ScionResearch/tof-proximity-sensor/src/web_server.cpp

#include "web_server.h"

WebServerManager::WebServerManager(ConfigManager* config_mgr, SensorManager* sensor_mgr) {
    config_manager = config_mgr;
    sensor_manager = sensor_mgr;
    server = new AsyncWebServer(80);
    dns_server = new DNSServer();
    session_count = 0;
    
    // Initialize session arrays
    for (int i = 0; i < 10; i++) {
        authenticated_sessions[i] = false;
        session_tokens[i] = "";
    }
}

WebServerManager::~WebServerManager() {
    delete server;
    delete dns_server;
}

bool WebServerManager::initialize() {
    // Set up basic routes
    server->on("/", HTTP_GET, [this](AsyncWebServerRequest* request) {
        handleRoot(request);
    });
    
    // iOS Captive Portal Detection routes
    server->on("/hotspot-detect.html", HTTP_GET, [this](AsyncWebServerRequest* request) {
        request->redirect("/");
    });
    
    server->on("/library/test/success.html", HTTP_GET, [this](AsyncWebServerRequest* request) {
        request->redirect("/");
    });
    
    server->on("/captive", HTTP_GET, [this](AsyncWebServerRequest* request) {
        request->redirect("/");
    });
    
    server->on("/generate_204", HTTP_GET, [this](AsyncWebServerRequest* request) {
        request->send(204);
    });
    
    server->on("/fwlink", HTTP_GET, [this](AsyncWebServerRequest* request) {
        request->redirect("/");
    });
    
    // Catch-all route for any other requests - redirect to main page
    server->onNotFound([this](AsyncWebServerRequest* request) {
        if (request->method() == HTTP_GET) {
            request->redirect("/");
        } else {
            request->send(404, "text/plain", "Not Found");
        }
    });
    
    server->on("/api/status", HTTP_GET, [this](AsyncWebServerRequest* request) {
        handleGetStatus(request);
    });
    
    server->on("/api/config", HTTP_GET, [this](AsyncWebServerRequest* request) {
        handleGetConfig(request);
    });
    
    server->on("/api/config", HTTP_POST, [this](AsyncWebServerRequest* request) {
        handleSetConfig(request);
    });
    
    server->on("/login", HTTP_GET, [this](AsyncWebServerRequest* request) {
        handleLogin(request);
    });
    
    server->on("/login", HTTP_POST, [this](AsyncWebServerRequest* request) {
        handleLogin(request);
    });
    
    server->on("/logout", HTTP_POST, [this](AsyncWebServerRequest* request) {
        handleLogout(request);
    });
    
    server->on("/api/change-password", HTTP_POST, [this](AsyncWebServerRequest* request) {
        handleChangePassword(request);
    });
    
    server->onNotFound([this](AsyncWebServerRequest* request) {
        handleNotFound(request);
    });
    
    // Initialize OTA functionality
    initializeOTA();
    
    // Start server
    server->begin();
    Serial.println("Web server started on port 80");
    return true;
}

bool WebServerManager::startAccessPoint() {
    // Get hardware MAC address before setting WiFi mode
    // Initialize WiFi first to ensure MAC address is available
    WiFi.mode(WIFI_OFF);
    delay(10);
    WiFi.mode(WIFI_STA);
    delay(100); // Give time for WiFi to initialize
    
    // Generate unique SSID based on MAC address
    uint8_t mac[6];
    WiFi.macAddress(mac);
    
    // Debug: Print full MAC address to verify uniqueness
    Serial.print("Hardware MAC Address: ");
    for (int i = 0; i < 6; i++) {
        if (i > 0) Serial.print(":");
        if (mac[i] < 16) Serial.print("0");
        Serial.print(mac[i], HEX);
    }
    Serial.println();
    
    // Use last 3 bytes for SSID (bytes 3, 4, 5)
    String unique_ssid = "ToF-Prox-";
    if (mac[3] < 16) unique_ssid += "0";
    unique_ssid += String(mac[3], HEX);
    if (mac[4] < 16) unique_ssid += "0";
    unique_ssid += String(mac[4], HEX);
    if (mac[5] < 16) unique_ssid += "0";
    unique_ssid += String(mac[5], HEX);
    unique_ssid.toUpperCase();
    
    WiFiConfig wifi_config = config_manager->getWiFiConfig();
    
    // Configure AP with specific settings for better iOS compatibility
    WiFi.mode(WIFI_AP);
    WiFi.softAPConfig(IPAddress(192, 168, 4, 1), IPAddress(192, 168, 4, 1), IPAddress(255, 255, 255, 0));
    
    // Start AP with specific settings: channel 1, no SSID hidden, max 4 connections
    bool success = WiFi.softAP(unique_ssid.c_str(), wifi_config.ap_password, 1, 0, 4);
    
    if (success) {
        // Additional iOS compatibility settings
        delay(100); // Small delay for AP to stabilize
        WiFi.softAPsetHostname("proximity-sensor");
    }
    
    if (success) {
        IPAddress ip = WiFi.softAPIP();
        Serial.print("Access Point started: ");
        Serial.println(unique_ssid);
        Serial.print("IP address: ");
        Serial.println(ip);
        
        // Start DNS server for captive portal
        dns_server->start(53, "*", ip);
        Serial.println("DNS server started for captive portal");
        
        return true;
    }
    
    Serial.println("Failed to start Access Point");
    return false;
}

void WebServerManager::stopAccessPoint() {
    WiFi.softAPdisconnect(true);
    Serial.println("Access Point stopped");
}

void WebServerManager::handleClient() {
    // Process DNS requests for captive portal
    dns_server->processNextRequest();
}

String WebServerManager::generateSessionToken() {
    String token = "";
    for (int i = 0; i < 16; i++) {
        token += String(random(0, 16), HEX);
    }
    return token;
}

void WebServerManager::addSession(const String& token) {
    for (int i = 0; i < 10; i++) {
        if (!authenticated_sessions[i]) {
            authenticated_sessions[i] = true;
            session_tokens[i] = token;
            session_count++;
            break;
        }
    }
}

bool WebServerManager::validateSession(const String& token) {
    for (int i = 0; i < 10; i++) {
        if (authenticated_sessions[i] && session_tokens[i] == token) {
            return true;
        }
    }
    return false;
}

bool WebServerManager::isAuthenticated(AsyncWebServerRequest* request) {
    if (request->hasHeader("Cookie")) {
        String cookie = request->header("Cookie");
        int tokenStart = cookie.indexOf("session_token=");
        if (tokenStart != -1) {
            tokenStart += 14; // Length of "session_token="
            int tokenEnd = cookie.indexOf(";", tokenStart);
            if (tokenEnd == -1) tokenEnd = cookie.length();
            String token = cookie.substring(tokenStart, tokenEnd);
            return validateSession(token);
        }
    }
    return false;
}

void WebServerManager::handleRoot(AsyncWebServerRequest* request) {
    if (!isAuthenticated(request)) {
        handleLogin(request);
        return;
    }
    
    String html = generateMainPage();
    AsyncWebServerResponse* response = request->beginResponse(200, "text/html", html);
    
    // Add iOS-friendly headers
    response->addHeader("Cache-Control", "no-cache, no-store, must-revalidate");
    response->addHeader("Pragma", "no-cache");
    response->addHeader("Expires", "0");
    response->addHeader("Connection", "close");
    
    request->send(response);
}

String WebServerManager::generateMainPage() {
    String html = "<!DOCTYPE html>";
    html += "<html><head><title>Proximity Sensor</title>";
    html += "<meta name='viewport' content='width=device-width, initial-scale=1'>";
    html += "<style>";
    html += "body { font-family: Arial; margin: 0; background:rgb(27, 27, 27); }";
    html += ".page-header { background:rgb(27, 27, 27); padding: 20px; text-align: center; }";
    html += ".header-logo img { max-width: 400px; height: auto; }";
    html += ".container { max-width: 800px; margin: 0 auto; background: white; padding: 20px; border-radius: 10px 10px 0 0; }";
    html += ".status-grid { display: grid; grid-template-columns: repeat(auto-fit, minmax(180px, 1fr)); gap: 15px; margin: 20px 0; }";
    html += ".status-card { background: #f8f9fa; padding: 15px; border-radius: 8px; text-align: center; border: 2px solid #e9ecef; min-height: 80px; display: flex; flex-direction: column; justify-content: center; }";
    html += ".status-value { font-size: 2em; font-weight: bold; color: #007bff; margin: 5px 0; }";
    html += ".refresh-btn { background: #007bff; color: white; border: none; padding: 10px 20px; border-radius: 5px; cursor: pointer; margin: 10px 5px; }";
    html += ".refresh-btn:hover { background: #0056b3; }";
    html += ".config-section { margin-top: 30px; padding: 20px; background: #f8f9fa; border-radius: 10px; }";
    html += ".output-config { margin: 20px 0; padding: 20px; background: white; border-radius: 8px; border: 1px solid #dee2e6; }";
    html += ".form-grid { display: grid; grid-template-columns: 1fr 200px; gap: 15px; align-items: center; margin: 12px 0; }";
    html += ".form-grid label { font-weight: bold; margin: 0; }";
    html += ".form-grid input, .form-grid select { width: 100%; padding: 8px; border: 1px solid #ced4da; border-radius: 4px; box-sizing: border-box; }";
    html += ".output-header { display: flex; align-items: center; justify-content: space-between; margin-bottom: 20px; padding-bottom: 10px; border-bottom: 2px solid #e9ecef; }";
    html += ".output-header h4 { margin: 0; color: #495057; }";
    html += ".enable-control { display: flex; align-items: center; gap: 10px; }";
    html += ".enable-control input[type='checkbox'] { transform: scale(1.3); margin: 0; }";
    html += ".config-btn { background: #28a745; color: white; border: none; padding: 12px 24px; border-radius: 5px; cursor: pointer; margin: 15px 5px; font-size: 16px; }";
    html += ".config-btn:hover { background: #218838; }";
    html += "#config-message { margin: 15px 0; padding: 10px; border-radius: 5px; display: none; }";
    html += ".success { background: #d4edda; color: #155724; border: 1px solid #c3e6cb; }";
    html += ".error { background: #f8d7da; color: #721c24; border: 1px solid #f5c6cb; }";
    html += ".logout-btn { background: #dc3545; color: white; border: none; padding: 8px 16px; border-radius: 5px; cursor: pointer; }";
    html += ".logout-btn:hover { background: #c82333; }";
    html += "@media (max-width: 600px) { .form-grid { grid-template-columns: 1fr; gap: 8px; } .form-grid label { margin-bottom: 5px; } .header-logo img { max-width: 400px; } }";
    html += "</style></head><body>";
    html += "<div class='page-header'>";
    html += "<div class='header-logo'>";
    html += "<img src=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 />";
    html += "</div>";
    html += "</div>";
    html += "<div class='container'>";
    html += "<h1>Proximity Sensor Monitor</h1>";
    html += "<div class='status-grid'>";
    html += "<div class='status-card'><h3>Distance</h3><div class='status-value' id='distance'>--</div><div>mm</div></div>";
    html += "<div class='status-card'><h3>Status</h3><div id='status'>--</div></div>";
    html += "<div class='status-card'><h3>Output 1</h3><div id='output1'>--</div></div>";
    html += "<div class='status-card'><h3>Output 2</h3><div id='output2'>--</div></div>";
    html += "</div>";
    html += "<div id='config-info'><h3>Current Configuration</h3><div id='config-display'>Loading...</div></div>";
    html += "<div class='config-section'>";
    html += "<h3>Output Configuration</h3>";
    html += "<form id='config-form'>";
    html += "<div class='output-config'>";
    html += "<div class='output-header'>";
    html += "<h4>Output 1</h4>";
    html += "<div class='enable-control'>";
    html += "<span>Enable</span>";
    html += "<input type='checkbox' id='output1_enabled' name='output1_enabled'>";
    html += "</div>";
    html += "</div>";
    html += "<div class='form-grid'>";
    html += "<label>Min Distance (mm):</label>";
    html += "<input type='number' id='output1_min' name='output1_min' min='0' max='4000'>";
    html += "</div>";
    html += "<div class='form-grid'>";
    html += "<label>Max Distance (mm):</label>";
    html += "<input type='number' id='output1_max' name='output1_max' min='0' max='4000'>";
    html += "</div>";
    html += "<div class='form-grid'>";
    html += "<label>Hysteresis (mm):</label>";
    html += "<input type='number' id='output1_hysteresis' name='output1_hysteresis' min='0' max='500'>";
    html += "</div>";
    html += "<div class='form-grid'>";
    html += "<label>Polarity:</label>";
    html += "<select id='output1_polarity' name='output1_polarity'><option value='in_range'>Active In Range</option><option value='out_range'>Active Out of Range</option></select>";
    html += "</div>";
    html += "</div>";
    html += "<div class='output-config'>";
    html += "<div class='output-header'>";
    html += "<h4>Output 2</h4>";
    html += "<div class='enable-control'>";
    html += "<span>Enable</span>";
    html += "<input type='checkbox' id='output2_enabled' name='output2_enabled'>";
    html += "</div>";
    html += "</div>";
    html += "<div class='form-grid'>";
    html += "<label>Min Distance (mm):</label>";
    html += "<input type='number' id='output2_min' name='output2_min' min='0' max='4000'>";
    html += "</div>";
    html += "<div class='form-grid'>";
    html += "<label>Max Distance (mm):</label>";
    html += "<input type='number' id='output2_max' name='output2_max' min='0' max='4000'>";
    html += "</div>";
    html += "<div class='form-grid'>";
    html += "<label>Hysteresis (mm):</label>";
    html += "<input type='number' id='output2_hysteresis' name='output2_hysteresis' min='0' max='500'>";
    html += "</div>";
    html += "<div class='form-grid'>";
    html += "<label>Polarity:</label>";
    html += "<select id='output2_polarity' name='output2_polarity'><option value='in_range'>Active In Range</option><option value='out_range'>Active Out of Range</option></select>";
    html += "</div>";
    html += "</div>";
    html += "<button type='button' class='config-btn' onclick='saveConfig()'>Save Configuration</button>";
    html += "</form>";
    html += "<div id='config-message'></div>";
    html += "</div>";
    html += "<div class='config-section'>";
    html += "<h3>Change Password</h3>";
    html += "<form id='password-form'>";
    html += "<div class='output-config'>";
    html += "<div class='form-grid'>";
    html += "<label>Current Password:</label>";
    html += "<input type='password' id='current_password' name='current_password' required>";
    html += "</div>";
    html += "<div class='form-grid'>";
    html += "<label>New Password:</label>";
    html += "<input type='password' id='new_password' name='new_password' required>";
    html += "</div>";
    html += "<div class='form-grid'>";
    html += "<label>Confirm New Password:</label>";
    html += "<input type='password' id='confirm_password' name='confirm_password' required>";
    html += "</div>";
    html += "<button type='button' class='config-btn' onclick='changePassword()'>Change Password</button>";
    html += "</div>";
    html += "</form>";
    html += "<div id='password-message'></div>";
    html += "</div>";
    html += "<div class='config-section'>";
    html += "<h3>Firmware Update (OTA)</h3>";
    html += "<div class='output-config'>";
    html += "<p style='color: #856404; background: #fff3cd; padding: 10px; border-radius: 5px; border: 1px solid #ffeaa7;'>";
    html += "<strong>Warning:</strong> Only upload firmware files (.bin) intended for this device. ";
    html += "Incorrect firmware can permanently damage the device.";
    html += "</p>";
    html += "<p><strong>Version:   </strong> " + String(FW_VERSION) + "</p>";
    html += "<p><strong>Build Date:</strong> " + String(__DATE__) + " " + String(__TIME__) + "</p>";
    html += "<button type='button' class='config-btn' onclick='openOTAUpdate()' style='background: #fd7e14;'>";
    html += "Open Firmware Update";
    html += "</button>";
    html += "</div>";
    html += "</div>";
    html += "<div style='text-align: center; margin-top: 30px; padding-top: 20px; border-top: 1px solid #dee2e6;'>";
    html += "<button class='logout-btn' onclick='logout()'>Logout</button>";
    html += "</div>";
    html += "</div>";
    html += "<script>";
    html += "function updateStatus() {";
    html += "fetch('/api/status').then(response => response.json()).then(data => {";
    html += "document.getElementById('distance').textContent = data.out_of_range ? 'Out of range' : data.distance;";
    html += "document.getElementById('status').textContent = data.status;";
    html += "document.getElementById('output1').textContent = data.output1_state ? 'ON' : 'OFF';";
    html += "document.getElementById('output2').textContent = data.output2_state ? 'ON' : 'OFF';";
    html += "const statusCard = document.getElementById('status').parentElement;";
    html += "const output1Card = document.getElementById('output1').parentElement;";
    html += "const output2Card = document.getElementById('output2').parentElement;";
    html += "if (data.status === 'OK') {";
    html += "statusCard.style.backgroundColor = '#e8f5e8';";
    html += "} else if (data.status === 'TRIGGERED') {";
    html += "statusCard.style.backgroundColor = '#e3f2fd';";
    html += "} else if (data.status === 'FAULT') {";
    html += "statusCard.style.backgroundColor = '#ffebee';";
    html += "} else {";
    html += "statusCard.style.backgroundColor = '#f8f9fa';";
    html += "}";
    html += "output1Card.style.backgroundColor = data.output1_state ? '#e3f2fd' : '#f8f9fa';";
    html += "output2Card.style.backgroundColor = data.output2_state ? '#e3f2fd' : '#f8f9fa';";
    html += "}).catch(error => console.error('Error:', error));";
    html += "}";
    html += "function loadConfig() {";
    html += "fetch('/api/config').then(response => response.json()).then(data => {";
    html += "const configHtml = '<p><strong>Device:</strong> ' + data.device_name + '</p>' +";
    html += "'<p><strong>Output 1:</strong> ' + (data.output1.enabled ? 'Enabled' : 'Disabled') + ' - ' + data.output1.min + '-' + data.output1.max + 'mm, Hyst: ' + data.output1.hysteresis + 'mm (' + (data.output1.active_in_range ? 'In Range' : 'Out of Range') + ')</p>' +";
    html += "'<p><strong>Output 2:</strong> ' + (data.output2.enabled ? 'Enabled' : 'Disabled') + ' - ' + data.output2.min + '-' + data.output2.max + 'mm, Hyst: ' + data.output2.hysteresis + 'mm (' + (data.output2.active_in_range ? 'In Range' : 'Out of Range') + ')</p>';";
    html += "document.getElementById('config-display').innerHTML = configHtml;";
    html += "document.getElementById('output1_enabled').checked = data.output1.enabled;";
    html += "document.getElementById('output1_min').value = data.output1.min;";
    html += "document.getElementById('output1_max').value = data.output1.max;";
    html += "document.getElementById('output1_hysteresis').value = data.output1.hysteresis;";
    html += "document.getElementById('output1_polarity').value = data.output1.active_in_range ? 'in_range' : 'out_range';";
    html += "document.getElementById('output2_enabled').checked = data.output2.enabled;";
    html += "document.getElementById('output2_min').value = data.output2.min;";
    html += "document.getElementById('output2_max').value = data.output2.max;";
    html += "document.getElementById('output2_hysteresis').value = data.output2.hysteresis;";
    html += "document.getElementById('output2_polarity').value = data.output2.active_in_range ? 'in_range' : 'out_range';";
    html += "}).catch(error => console.error('Error:', error));";
    html += "}";
    html += "function saveConfig() {";
    html += "const formData = new FormData();";
    html += "formData.append('output1_enabled', document.getElementById('output1_enabled').checked ? '1' : '0');";
    html += "formData.append('output1_min', document.getElementById('output1_min').value);";
    html += "formData.append('output1_max', document.getElementById('output1_max').value);";
    html += "formData.append('output1_hysteresis', document.getElementById('output1_hysteresis').value);";
    html += "formData.append('output1_polarity', document.getElementById('output1_polarity').value);";
    html += "formData.append('output2_enabled', document.getElementById('output2_enabled').checked ? '1' : '0');";
    html += "formData.append('output2_min', document.getElementById('output2_min').value);";
    html += "formData.append('output2_max', document.getElementById('output2_max').value);";
    html += "formData.append('output2_hysteresis', document.getElementById('output2_hysteresis').value);";
    html += "formData.append('output2_polarity', document.getElementById('output2_polarity').value);";
    html += "fetch('/api/config', { method: 'POST', body: formData })";
    html += ".then(response => response.json()).then(data => {";
    html += "const msgDiv = document.getElementById('config-message');";
    html += "msgDiv.style.display = 'block';";
    html += "if (data.status === 'success') {";
    html += "msgDiv.className = 'success';";
    html += "msgDiv.textContent = 'Configuration saved successfully!';";
    html += "loadConfig();";
    html += "} else {";
    html += "msgDiv.className = 'error';";
    html += "msgDiv.textContent = 'Error: ' + data.message;";
    html += "}";
    html += "setTimeout(() => msgDiv.style.display = 'none', 3000);";
    html += "}).catch(error => {";
    html += "const msgDiv = document.getElementById('config-message');";
    html += "msgDiv.style.display = 'block';";
    html += "msgDiv.className = 'error';";
    html += "msgDiv.textContent = 'Network error: ' + error.message;";
    html += "setTimeout(() => msgDiv.style.display = 'none', 3000);";
    html += "});";
    html += "}";
    html += "function logout() {";
    html += "fetch('/logout', { method: 'POST' }).then(() => {";
    html += "window.location.href = '/login';";
    html += "});";
    html += "}";
    html += "function changePassword() {";
    html += "const newPassword = document.getElementById('new_password').value;";
    html += "const confirmPassword = document.getElementById('confirm_password').value;";
    html += "if (newPassword !== confirmPassword) {";
    html += "const msgDiv = document.getElementById('password-message');";
    html += "msgDiv.style.display = 'block';";
    html += "msgDiv.className = 'error';";
    html += "msgDiv.textContent = 'New passwords do not match!';";
    html += "setTimeout(() => msgDiv.style.display = 'none', 3000);";
    html += "return;";
    html += "}";
    html += "const formData = new FormData();";
    html += "formData.append('current_password', document.getElementById('current_password').value);";
    html += "formData.append('new_password', newPassword);";
    html += "fetch('/api/change-password', { method: 'POST', body: formData })";
    html += ".then(response => response.json()).then(data => {";
    html += "const msgDiv = document.getElementById('password-message');";
    html += "msgDiv.style.display = 'block';";
    html += "if (data.status === 'success') {";
    html += "msgDiv.className = 'success';";
    html += "msgDiv.textContent = 'Password changed successfully!';";
    html += "document.getElementById('current_password').value = '';";
    html += "document.getElementById('new_password').value = '';";
    html += "document.getElementById('confirm_password').value = '';";
    html += "} else {";
    html += "msgDiv.className = 'error';";
    html += "msgDiv.textContent = 'Error: ' + data.message;";
    html += "}";
    html += "setTimeout(() => msgDiv.style.display = 'none', 3000);";
    html += "}).catch(error => {";
    html += "const msgDiv = document.getElementById('password-message');";
    html += "msgDiv.style.display = 'block';";
    html += "msgDiv.className = 'error';";
    html += "msgDiv.textContent = 'Network error: ' + error.message;";
    html += "setTimeout(() => msgDiv.style.display = 'none', 3000);";
    html += "});";
    html += "}";
    html += "function openOTAUpdate() {";
    html += "if (confirm('Are you sure you want to open the firmware update page? Make sure you have the correct firmware file ready.')) {";
    html += "window.open('/update', '_blank');";
    html += "}";
    html += "}";
    html += "function detectMobileAndHideFirmware() {";
    html += "const userAgent = navigator.userAgent.toLowerCase();";
    html += "const isMobile = /android|webos|iphone|ipad|ipod|blackberry|iemobile|opera mini|mobile/.test(userAgent);";
    html += "const firmwareSections = document.querySelectorAll('.config-section');";
    html += "for(let section of firmwareSections) {";
    html += "if(section.innerHTML.includes('Firmware Update')) {";
    html += "if(isMobile) section.style.display = 'none';";
    html += "break;";
    html += "}";
    html += "}";
    html += "}";
    html += "detectMobileAndHideFirmware();";
    html += "setInterval(updateStatus, 200);";
    html += "updateStatus(); loadConfig();";
    html += "</script></body></html>";
    
    return html;
}

void WebServerManager::handleGetStatus(AsyncWebServerRequest* request) {
    if (!isAuthenticated(request)) {
        request->send(401, "application/json", "{\"error\":\"Unauthorized\"}");
        return;
    }
    
    JsonDocument doc;
    doc["distance"] = sensor_manager->getDistance();
    doc["raw_distance"] = sensor_manager->getRawDistance();
    doc["sensor_ready"] = sensor_manager->isSensorReady();
    doc["out_of_range"] = sensor_manager->isOutOfRange();
    
    switch (sensor_manager->getStatus()) {
        case STATUS_OK:
            doc["status"] = "OK";
            break;
        case STATUS_TRIGGERED:
            doc["status"] = "TRIGGERED";
            break;
        case STATUS_FAULT:
            doc["status"] = "FAULT";
            break;
    }
    
    doc["output1_state"] = sensor_manager->getOutput1Config().current_state;
    doc["output2_state"] = sensor_manager->getOutput2Config().current_state;
    doc["timestamp"] = millis();
    
    String response;
    serializeJson(doc, response);
    AsyncWebServerResponse* res = request->beginResponse(200, "application/json", response);
    res->addHeader("Cache-Control", "no-cache, no-store, must-revalidate");
    res->addHeader("Pragma", "no-cache");
    res->addHeader("Expires", "0");
    res->addHeader("Connection", "close");
    request->send(res);
}

void WebServerManager::handleGetConfig(AsyncWebServerRequest* request) {
    if (!isAuthenticated(request)) {
        request->send(401, "application/json", "{\"error\":\"Unauthorized\"}");
        return;
    }
    
    String config = config_manager->getConfigJson();
    AsyncWebServerResponse* res = request->beginResponse(200, "application/json", config);
    res->addHeader("Cache-Control", "no-cache, no-store, must-revalidate");
    res->addHeader("Pragma", "no-cache");
    res->addHeader("Expires", "0");
    res->addHeader("Connection", "close");
    request->send(res);
}

void WebServerManager::handleNotFound(AsyncWebServerRequest* request) {
    request->send(404, "text/plain", "Not Found");
}

void WebServerManager::handleLogin(AsyncWebServerRequest* request) {
    if (request->method() == HTTP_GET) {
        // Show login form
        String html = "<!DOCTYPE html><html><head><title>Login - Proximity Sensor</title>";
        html += "<meta name='viewport' content='width=device-width, initial-scale=1'>";
        html += "<style>";
        html += "body { font-family: Arial; margin: 0; padding: 0; background: #f0f0f0; display: flex; justify-content: center; align-items: center; min-height: 100vh; }";
        html += ".login-container { background: white; padding: 40px; border-radius: 10px; box-shadow: 0 4px 6px rgba(0,0,0,0.1); max-width: 400px; width: 100%; }";
        html += "h1 { text-align: center; color: #333; margin-bottom: 30px; }";
        html += "label { display: block; margin: 15px 0 5px; font-weight: bold; }";
        html += "input[type='password'] { width: 100%; padding: 12px; border: 1px solid #ddd; border-radius: 5px; font-size: 16px; box-sizing: border-box; }";
        html += ".login-btn { width: 100%; background: #007bff; color: white; border: none; padding: 12px; border-radius: 5px; font-size: 16px; cursor: pointer; margin-top: 20px; }";
        html += ".login-btn:hover { background: #0056b3; }";
        html += ".error { color: #dc3545; text-align: center; margin-top: 15px; }";
        html += "</style></head><body>";
        html += "<div class='login-container'>";
        html += "<h1>Proximity Sensor Login</h1>";
        html += "<form method='POST' action='/login'>";
        html += "<label for='password'>Password:</label>";
        html += "<input type='password' id='password' name='password' required>";
        html += "<button type='submit' class='login-btn'>Login</button>";
        html += "</form>";
        if (request->hasParam("error")) {
            html += "<div class='error'>Invalid password. Please try again.</div>";
        }
        html += "</div></body></html>";
        
        AsyncWebServerResponse* response = request->beginResponse(200, "text/html", html);
        // Add iOS-friendly headers
        response->addHeader("Cache-Control", "no-cache, no-store, must-revalidate");
        response->addHeader("Pragma", "no-cache");
        response->addHeader("Expires", "0");
        response->addHeader("Connection", "close");
        request->send(response);
    } else {
        // Process login
        if (request->hasParam("password", true)) {
            String password = request->getParam("password", true)->value();
            WiFiConfig wifi_config = config_manager->getWiFiConfig();
            
            if (password == wifi_config.admin_password) {
                // Generate session token
                String token = generateSessionToken();
                addSession(token);
                
                // Set cookie and redirect
                AsyncWebServerResponse* response = request->beginResponse(302);
                response->addHeader("Location", "/");
                response->addHeader("Set-Cookie", "session_token=" + token + "; Path=/; HttpOnly");
                request->send(response);
            } else {
                request->redirect("/login?error=1");
            }
        } else {
            request->redirect("/login?error=1");
        }
    }
}

void WebServerManager::handleLogout(AsyncWebServerRequest* request) {
    // Clear session
    if (request->hasHeader("Cookie")) {
        String cookie = request->header("Cookie");
        int tokenStart = cookie.indexOf("session_token=");
        if (tokenStart != -1) {
            tokenStart += 14;
            int tokenEnd = cookie.indexOf(";", tokenStart);
            if (tokenEnd == -1) tokenEnd = cookie.length();
            String token = cookie.substring(tokenStart, tokenEnd);
            
            // Remove session
            for (int i = 0; i < 10; i++) {
                if (session_tokens[i] == token) {
                    authenticated_sessions[i] = false;
                    session_tokens[i] = "";
                    break;
                }
            }
        }
    }
    
    // Clear cookie and redirect
    AsyncWebServerResponse* response = request->beginResponse(302);
    response->addHeader("Location", "/login");
    response->addHeader("Set-Cookie", "session_token=; Path=/; HttpOnly; Max-Age=0");
    request->send(response);
}

void WebServerManager::handleChangePassword(AsyncWebServerRequest* request) {
    if (!isAuthenticated(request)) {
        request->send(401, "application/json", "{\"error\":\"Unauthorized\"}");
        return;
    }
    
    if (request->hasParam("current_password", true) && request->hasParam("new_password", true)) {
        String current_password = request->getParam("current_password", true)->value();
        String new_password = request->getParam("new_password", true)->value();
        
        WiFiConfig wifi_config = config_manager->getWiFiConfig();
        
        if (current_password == wifi_config.admin_password) {
            wifi_config.admin_password = new_password;
            config_manager->setWiFiConfig(wifi_config);
            config_manager->saveConfig();
            
            Serial.println("Admin password changed via web interface");
            request->send(200, "application/json", "{\"status\":\"success\",\"message\":\"Password changed successfully\"}");
        } else {
            request->send(400, "application/json", "{\"status\":\"error\",\"message\":\"Current password is incorrect\"}");
        }
    } else {
        request->send(400, "application/json", "{\"status\":\"error\",\"message\":\"Missing required parameters\"}");
    }
}
void WebServerManager::handleSetConfig(AsyncWebServerRequest* request) {
    if (!isAuthenticated(request)) {
        request->send(401, "application/json", "{\"error\":\"Unauthorized\"}");
        return;
    }
    
    // Parse form data from POST request
    bool config_changed = false;
    DeviceConfig current_config = config_manager->getDeviceConfig();
    
    // Output 1 configuration
    if (request->hasParam("output1_enabled", true)) {
        bool new_enabled = request->getParam("output1_enabled", true)->value() == "1";
        if (new_enabled != current_config.output1_enabled) {
            current_config.output1_enabled = new_enabled;
            config_changed = true;
        }
    }
    
    if (request->hasParam("output1_min", true)) {
        int new_min = request->getParam("output1_min", true)->value().toInt();
        if (new_min != current_config.output1_min) {
            current_config.output1_min = new_min;
            config_changed = true;
        }
    }
    
    if (request->hasParam("output1_max", true)) {
        int new_max = request->getParam("output1_max", true)->value().toInt();
        if (new_max != current_config.output1_max) {
            current_config.output1_max = new_max;
            config_changed = true;
        }
    }
    
    if (request->hasParam("output1_hysteresis", true)) {
        int new_hyst = request->getParam("output1_hysteresis", true)->value().toInt();
        if (new_hyst != current_config.output1_hysteresis) {
            current_config.output1_hysteresis = new_hyst;
            config_changed = true;
        }
    }
    
    if (request->hasParam("output1_polarity", true)) {
        bool new_polarity = request->getParam("output1_polarity", true)->value() == "in_range";
        if (new_polarity != current_config.output1_active_in_range) {
            current_config.output1_active_in_range = new_polarity;
            config_changed = true;
        }
    }
    
    // Output 2 configuration
    if (request->hasParam("output2_enabled", true)) {
        bool new_enabled = request->getParam("output2_enabled", true)->value() == "1";
        if (new_enabled != current_config.output2_enabled) {
            current_config.output2_enabled = new_enabled;
            config_changed = true;
        }
    }
    
    if (request->hasParam("output2_min", true)) {
        int new_min = request->getParam("output2_min", true)->value().toInt();
        if (new_min != current_config.output2_min) {
            current_config.output2_min = new_min;
            config_changed = true;
        }
    }
    
    if (request->hasParam("output2_max", true)) {
        int new_max = request->getParam("output2_max", true)->value().toInt();
        if (new_max != current_config.output2_max) {
            current_config.output2_max = new_max;
            config_changed = true;
        }
    }
    
    if (request->hasParam("output2_hysteresis", true)) {
        int new_hyst = request->getParam("output2_hysteresis", true)->value().toInt();
        if (new_hyst != current_config.output2_hysteresis) {
            current_config.output2_hysteresis = new_hyst;
            config_changed = true;
        }
    }
    
    if (request->hasParam("output2_polarity", true)) {
        bool new_polarity = request->getParam("output2_polarity", true)->value() == "in_range";
        if (new_polarity != current_config.output2_active_in_range) {
            current_config.output2_active_in_range = new_polarity;
            config_changed = true;
        }
    }
    
    // Apply changes if any were made
    if (config_changed) {
        config_manager->setDeviceConfig(current_config);
        config_manager->saveConfig();
        
        // Update sensor manager with new configuration
        sensor_manager->updateConfiguration(current_config);
        
        Serial.println("Configuration updated via web interface");
        request->send(200, "application/json", "{\"status\":\"success\",\"message\":\"Configuration updated\"}");
    } else {
        request->send(200, "application/json", "{\"status\":\"no_change\",\"message\":\"No changes detected\"}");
    }
}
void WebServerManager::handleGetHistory(AsyncWebServerRequest* request) {}
void WebServerManager::handleClearHistory(AsyncWebServerRequest* request) {}
void WebServerManager::handleResetConfig(AsyncWebServerRequest* request) {}

// OTA Update Implementation
void WebServerManager::initializeOTA() {
    // Add OTA update page route
    server->on("/update", HTTP_GET, [this](AsyncWebServerRequest* request) {
        handleOTAUpdate(request);
    });
    
    // Add OTA upload handler
    server->on("/update", HTTP_POST, 
        [this](AsyncWebServerRequest* request) {
            // Handle the response after upload completes
            if (Update.hasError()) {
                request->send(500, "text/plain", "Update Failed: " + String(Update.getError()));
            } else {
                request->send(200, "text/plain", "Update Successful! Rebooting...");
                delay(1000);
                ESP.restart();
            }
        },
        [this](AsyncWebServerRequest* request, String filename, size_t index, uint8_t* data, size_t len, bool final) {
            handleOTAUpload(request, filename, index, data, len, final);
        }
    );
    
    Serial.println("OTA Update service initialized");
    Serial.println("Access OTA update at: http://[device-ip]/update");
}

void WebServerManager::handleOTAUpdate(AsyncWebServerRequest* request) {
    // Check authentication
    if (!isAuthenticated(request)) {
        request->redirect("/login");
        return;
    }
    
    // Generate OTA update page
    String html = "<!DOCTYPE html><html><head>";
    html += "<title>Firmware Update - Proximity Sensor</title>";
    html += "<meta name='viewport' content='width=device-width, initial-scale=1'>";
    html += "<style>";
    html += "body { font-family: Arial, sans-serif; margin: 0; padding: 20px; background: #f5f5f5; }";
    html += ".container { max-width: 600px; margin: 0 auto; background: white; padding: 30px; border-radius: 10px; box-shadow: 0 2px 10px rgba(0,0,0,0.1); }";
    html += "h1 { color: #333; text-align: center; margin-bottom: 30px; }";
    html += ".warning { background: #fff3cd; color: #856404; padding: 15px; border-radius: 5px; border: 1px solid #ffeaa7; margin-bottom: 20px; }";
    html += ".upload-section { background: #f8f9fa; padding: 20px; border-radius: 5px; margin: 20px 0; }";
    html += "input[type='file'] { width: 100%; padding: 10px; margin: 10px 0; border: 2px dashed #ccc; border-radius: 5px; }";
    html += ".btn { background: #007bff; color: white; border: none; padding: 12px 24px; border-radius: 5px; cursor: pointer; font-size: 16px; width: 100%; }";
    html += ".btn:hover { background: #0056b3; }";
    html += ".btn:disabled { background: #6c757d; cursor: not-allowed; }";
    html += "#progress { width: 100%; height: 20px; background: #e9ecef; border-radius: 10px; margin: 20px 0; overflow: hidden; }";
    html += "#progress-bar { height: 100%; background: #28a745; width: 0%; transition: width 0.3s; }";
    html += ".back-btn { background: #6c757d; margin-top: 20px; }";
    html += ".back-btn:hover { background: #545b62; }";
    html += "</style></head><body>";
    html += "<div class='container'>";
    html += "<h1>Firmware Update</h1>";
    html += "<div class='warning'>";
    html += "<strong>Warning:</strong> Only upload firmware files (.bin) intended for this device. ";
    html += "Incorrect firmware can permanently damage the device. Ensure you have a stable power supply during the update.";
    html += "</div>";
    html += "<div class='upload-section'>";
    html += "<h3>Current Firmware</h3>";
    html += "<p><strong>Version:   </strong> " + String(FW_VERSION) + "</p>";
    html += "<p><strong>Build Date:</strong> " + String(__DATE__) + " " + String(__TIME__) + "</p>";
    html += "<p><strong>Free Space:</strong> " + String(ESP.getFreeSketchSpace()) + " bytes</p>";
    html += "</div>";
    html += "<form id='upload-form' enctype='multipart/form-data'>";
    html += "<h3>Select Firmware File</h3>";
    html += "<input type='file' id='firmware-file' accept='.bin' required>";
    html += "<button type='submit' class='btn' id='upload-btn'>Upload Firmware</button>";
    html += "</form>";
    html += "<div id='progress' style='display: none;'>";
    html += "<div id='progress-bar'></div>";
    html += "</div>";
    html += "<div id='status'></div>";
    html += "<button class='btn back-btn' onclick='window.close()'>Close Window</button>";
    html += "</div>";
    html += "<script>";
    html += "document.getElementById('upload-form').addEventListener('submit', function(e) {";
    html += "e.preventDefault();";
    html += "const fileInput = document.getElementById('firmware-file');";
    html += "const file = fileInput.files[0];";
    html += "if (!file) { alert('Please select a firmware file'); return; }";
    html += "if (!file.name.endsWith('.bin')) { alert('Please select a .bin file'); return; }";
    html += "uploadFirmware(file);";
    html += "});";
    html += "function uploadFirmware(file) {";
    html += "const formData = new FormData();";
    html += "formData.append('firmware', file);";
    html += "const xhr = new XMLHttpRequest();";
    html += "document.getElementById('progress').style.display = 'block';";
    html += "document.getElementById('upload-btn').disabled = true;";
    html += "document.getElementById('upload-btn').textContent = 'Uploading...';";
    html += "xhr.upload.addEventListener('progress', function(e) {";
    html += "if (e.lengthComputable) {";
    html += "const percent = (e.loaded / e.total) * 100;";
    html += "document.getElementById('progress-bar').style.width = percent + '%';";
    html += "document.getElementById('status').innerHTML = '<p>Uploading: ' + Math.round(percent) + '%</p>';";
    html += "}";
    html += "});";
    html += "xhr.addEventListener('load', function() {";
    html += "if (xhr.status === 200) {";
    html += "document.getElementById('status').innerHTML = '<p style=\"color: green;\">Upload successful! Device is rebooting...</p>';";
    html += "setTimeout(() => { window.close(); }, 3000);";
    html += "} else {";
    html += "document.getElementById('status').innerHTML = '<p style=\"color: red;\">Upload failed: ' + xhr.responseText + '</p>';";
    html += "document.getElementById('upload-btn').disabled = false;";
    html += "document.getElementById('upload-btn').textContent = 'Upload Firmware';";
    html += "}";
    html += "});";
    html += "xhr.addEventListener('error', function() {";
    html += "document.getElementById('status').innerHTML = '<p style=\"color: red;\">Network error during upload</p>';";
    html += "document.getElementById('upload-btn').disabled = false;";
    html += "document.getElementById('upload-btn').textContent = 'Upload Firmware';";
    html += "});";
    html += "xhr.open('POST', '/update');";
    html += "xhr.send(formData);";
    html += "}";
    html += "</script></body></html>";
    
    request->send(200, "text/html", html);
}

void WebServerManager::handleOTAUpload(AsyncWebServerRequest* request, String filename, size_t index, uint8_t* data, size_t len, bool final) {
    if (!index) {
        Serial.printf("OTA Update Start: %s\n", filename.c_str());
        
        // Set LED to firmware update mode (orange)
        sensor_manager->setOTAUpdateMode(true);
        
        // Basic security validation
        if (!filename.endsWith(".bin")) {
            Serial.println("[SECURITY] Invalid file extension - only .bin files allowed");
            sensor_manager->setOTAUpdateMode(false);
            return;
        }
        
        // Check available space
        size_t free_space = ESP.getFreeSketchSpace();
        Serial.printf("[SECURITY] Available space: %u bytes\n", free_space);
        
        if (free_space < 100000) { // Minimum 100KB required
            Serial.println("[SECURITY] Insufficient free space for firmware update");
            sensor_manager->setOTAUpdateMode(false);
            return;
        }
        
        // Start the update process
        if (!Update.begin(UPDATE_SIZE_UNKNOWN)) {
            Serial.printf("Update Begin Error: %s\n", Update.errorString());
            sensor_manager->setOTAUpdateMode(false);
            return;
        }
        
        Serial.println("[OTA] Firmware update started - LED set to orange");
    }
    
    // Write the received data
    if (Update.write(data, len) != len) {
        Serial.printf("Update Write Error: %s\n", Update.errorString());
        sensor_manager->setOTAUpdateMode(false);
        return;
    }
    
    // Print progress
    Serial.printf("OTA Progress: %u bytes\n", index + len);
    
    if (final) {
        // Additional security validation before finalizing
        size_t total_size = index + len;
        Serial.printf("[SECURITY] Total firmware size: %u bytes\n", total_size);
        
        // Check minimum firmware size (reasonable firmware should be at least 200KB)
        if (total_size < 200000) {
            Serial.println("[SECURITY] Firmware too small - possible invalid file");
            Update.abort();
            sensor_manager->setOTAUpdateMode(false);
            return;
        }
        
        // Check maximum firmware size (prevent oversized uploads)
        if (total_size > ESP.getFreeSketchSpace()) {
            Serial.println("[SECURITY] Firmware too large for available space");
            Update.abort();
            sensor_manager->setOTAUpdateMode(false);
            return;
        }
        
        // Finalize the update
        if (Update.end(true)) {
            Serial.printf("[OTA] Update Success: %u bytes\n", total_size);
            Serial.println("[OTA] Firmware validation passed - rebooting in 2 seconds");
            
            // Keep LED in update mode briefly to show success
            delay(2000);
            
            // Reset LED before reboot
            sensor_manager->setOTAUpdateMode(false);
            
            Serial.println("[OTA] Rebooting now...");
        } else {
            Serial.printf("[OTA] Update End Error: %s\n", Update.errorString());
            Serial.println("[SECURITY] Firmware validation failed");
            sensor_manager->setOTAUpdateMode(false);
        }
    }
}
